Quentis/kee_smart_opener/sw/efr32fg23/config/app_button_press_config.h

/***************************************************************************//**
 * @file
 * @brief
 *******************************************************************************
 * # License
 * <b>Copyright 2021 Silicon Laboratories Inc. www.silabs.com</b>
 *******************************************************************************
 *
 * SPDX-License-Identifier: Zlib
 *
 * The licensor of this software is Silicon Laboratories Inc.
 *
 * This software is provided 'as-is', without any express or implied
 * warranty. In no event will the authors be held liable for any damages
 * arising from the use of this software.
 *
 * Permission is granted to anyone to use this software for any purpose,
 * including commercial applications, and to alter it and redistribute it
 * freely, subject to the following restrictions:
 *
 * 1. The origin of this software must not be misrepresented; you must not
 *    claim that you wrote the original software. If you use this software
 *    in a product, an acknowledgment in the product documentation would be
 *    appreciated but is not required.
 * 2. Altered source versions must be plainly marked as such, and must not be
 *    misrepresented as being the original software.
 * 3. This notice may not be removed or altered from any source distribution.
 *
 ******************************************************************************/
#ifndef APP_BUTTON_PRESS_CONFIG_H
#define APP_BUTTON_PRESS_CONFIG_H

#define APP_BUTTON_PRESS_DETECT_RELEASE (0U)
#define APP_BUTTON_PRESS_DETECT_PRESS_AND_RELEASE (1U)

// <<< Use Configuration Wizard in Context Menu >>>

// <h> Edge Detection

// <o APP_BUTTON_PRESS_DETECTION> Button events to detect by the component
// <APP_BUTTON_PRESS_DETECT_RELEASE=> Button release detection
// <APP_BUTTON_PRESS_DETECT_PRESS_AND_RELEASE=> Button press and release detection
// <i> Default: Button release detection
// <i> By changing this configuration to detect press and release it is necessary to
// increase the command queue size of this component, since more events need to be handled.
#define APP_BUTTON_PRESS_DETECTION      APP_BUTTON_PRESS_DETECT_RELEASE

// </h>

// <h> Threshold values

// <o MIN_VALID_BUTTON_PRESS_DURATION_MS> Minimum duration (ms) of valid button presses
// <i> Default: 40
// <i> Any button press shorter than this value will not be considered as a valid button
// press.
#define MIN_VALID_BUTTON_PRESS_DURATION_MS    (40)

// <o SHORT_BUTTON_PRESS_DURATION_MS> Duration (ms) of Short button presses
// <i> Default: 250
// <i> Any button press shorter than this value and longer than MIN_VALID_BUTTON_PRESS_DURATION_MS
// will be considered SHORT_BUTTON_PRESS.
#define SHORT_BUTTON_PRESS_DURATION_MS   (250)

// <o MEDIUM_BUTTON_PRESS_DURATION_MS> Duration (ms) of MEDIUM button presses
// <i> Default: 1000
// <i> Any button press shorter than this value and longer SHORT_BUTTON_PRESS than will
// be considered MEDIUM_BUTTON_PRESS.
#define MEDIUM_BUTTON_PRESS_DURATION_MS   (1000)

// <o LONG_BUTTON_PRESS_DURATION_MS> Duration (ms) of LONG button presses
// <i> Default: 5000
// <i> Any button press shorter than this value and longer MEDIUM_BUTTON_PRESS than will
// be consideredLONG_BUTTON_PRESS. Any button press longer than this value will be
// considered VERY_LONG_BUTTON_PRESS
#define LONG_BUTTON_PRESS_DURATION_MS   (5000)

// <o APP_BUTTON_PRESS_WAKEUP_DELAY_MS> Duration (ms) from the button press wakeup interrupt to the Sleep Timer initialization
// <i> Default: 0
// <i> This value will be added to the button press timestamp if it caused a wakeup from EM4.
#define APP_BUTTON_PRESS_WAKEUP_DELAY_MS   (0)

// </h>

// <h> Runtime Adaptation

// <o APP_BUTTON_PRESS_CONFIG_PRIORITY> Runtime context priority
// <APP_RTA_PRIORITY_LOW=> Low
// <APP_RTA_PRIORITY_BELOW_NORMAL=> Below normal
// <APP_RTA_PRIORITY_NORMAL=> Normal
// <APP_RTA_PRIORITY_ABOVE_NORMAL=> Above normal
// <APP_RTA_PRIORITY_HIGH=> High
// <i> Default: Normal
// <i> Only takes effect for RTOS.
#define APP_BUTTON_PRESS_CONFIG_PRIORITY           APP_RTA_PRIORITY_NORMAL

// <o APP_BUTTON_PRESS_CONFIG_STACK_SIZE> Stack size (in bytes)
// <i> Default: 1024
// <i> Only takes effect for RTOS.
#define APP_BUTTON_PRESS_CONFIG_STACK_SIZE         (1024)

// <o APP_BUTTON_PRESS_CONFIG_WAIT_FOR_GUARD> Timeout for guard (in ticks)
// <i> Default: 5
// <i> Only takes effect for RTOS.
#define APP_BUTTON_PRESS_CONFIG_WAIT_FOR_GUARD     (5)

// <o APP_BUTTON_PRESS_CONFIG_QUEUE_SIZE> Queue size
// <i> Default: 4
// <i> Queue size for all (bare-metal and RTOS) adaptations.
#define APP_BUTTON_PRESS_CONFIG_QUEUE_SIZE         (4)

// </h>

// <<< end of configuration section >>>

#endif // APP_BUTTON_PRESS_CONFIG_H
