Quentis/kee_smart_opener/sw/efr32fg23/config/pin_config.h

#ifndef PIN_CONFIG_H
#define PIN_CONFIG_H

// $[CMU]
// [CMU]$

// $[LFXO]
// [LFXO]$

// $[PRS.ASYNCH0]
// [PRS.ASYNCH0]$

// $[PRS.ASYNCH1]
// [PRS.ASYNCH1]$

// $[PRS.ASYNCH2]
// [PRS.ASYNCH2]$

// $[PRS.ASYNCH3]
// [PRS.ASYNCH3]$

// $[PRS.ASYNCH4]
// [PRS.ASYNCH4]$

// $[PRS.ASYNCH5]
// [PRS.ASYNCH5]$

// $[PRS.ASYNCH6]
// [PRS.ASYNCH6]$

// $[PRS.ASYNCH7]
// [PRS.ASYNCH7]$

// $[PRS.ASYNCH8]
// [PRS.ASYNCH8]$

// $[PRS.ASYNCH9]
// [PRS.ASYNCH9]$

// $[PRS.ASYNCH10]
// [PRS.ASYNCH10]$

// $[PRS.ASYNCH11]
// [PRS.ASYNCH11]$

// $[PRS.SYNCH0]
// [PRS.SYNCH0]$

// $[PRS.SYNCH1]
// [PRS.SYNCH1]$

// $[PRS.SYNCH2]
// [PRS.SYNCH2]$

// $[PRS.SYNCH3]
// [PRS.SYNCH3]$

// $[GPIO]
// GPIO SWV on PA03
#ifndef GPIO_SWV_PORT                           
#define GPIO_SWV_PORT                            SL_GPIO_PORT_A
#endif
#ifndef GPIO_SWV_PIN                            
#define GPIO_SWV_PIN                             3
#endif

// [GPIO]$

// $[TIMER0]
// TIMER0 CC0 on PD02
#ifndef TIMER0_CC0_PORT                         
#define TIMER0_CC0_PORT                          SL_GPIO_PORT_D
#endif
#ifndef TIMER0_CC0_PIN                          
#define TIMER0_CC0_PIN                           2
#endif

// [TIMER0]$

// $[TIMER1]
// [TIMER1]$

// $[TIMER2]
// [TIMER2]$

// $[TIMER3]
// [TIMER3]$

// $[TIMER4]
// [TIMER4]$

// $[USART0]
// [USART0]$

// $[I2C1]
// [I2C1]$

// $[EUSART1]
// [EUSART1]$

// $[EUSART2]
// [EUSART2]$

// $[LCD]
// [LCD]$

// $[KEYSCAN]
// [KEYSCAN]$

// $[LETIMER0]
// [LETIMER0]$

// $[IADC0]
// [IADC0]$

// $[ACMP0]
// [ACMP0]$

// $[ACMP1]
// [ACMP1]$

// $[VDAC0]
// [VDAC0]$

// $[PCNT0]
// [PCNT0]$

// $[LESENSE]
// [LESENSE]$

// $[HFXO0]
// [HFXO0]$

// $[I2C0]
// [I2C0]$

// $[EUSART0]
// [EUSART0]$

// $[PTI]
// [PTI]$

// $[MODEM]
// [MODEM]$

// $[CUSTOM_PIN_NAME]
#ifndef _PORT                                   
#define _PORT                                    SL_GPIO_PORT_A
#endif
#ifndef _PIN                                    
#define _PIN                                     0
#endif































// [CUSTOM_PIN_NAME]$


#endif // PIN_CONFIG_H
