Quentis/kee_smart_opener/sw/efr32fg23/config/sl_rail_util_init_inst0_config.h

/***************************************************************************//**
 * @file
 * @brief
 *******************************************************************************
 * # License
 * <b>Copyright 2024 Silicon Laboratories Inc. www.silabs.com</b>
 *******************************************************************************
 *
 * SPDX-License-Identifier: Zlib
 *
 * The licensor of this software is Silicon Laboratories Inc.
 *
 * This software is provided 'as-is', without any express or implied
 * warranty. In no event will the authors be held liable for any damages
 * arising from the use of this software.
 *
 * Permission is granted to anyone to use this software for any purpose,
 * including commercial applications, and to alter it and redistribute it
 * freely, subject to the following restrictions:
 *
 * 1. The origin of this software must not be misrepresented; you must not
 *    claim that you wrote the original software. If you use this software
 *    in a product, an acknowledgment in the product documentation would be
 *    appreciated but is not required.
 * 2. Altered source versions must be plainly marked as such, and must not be
 *    misrepresented as being the original software.
 * 3. This notice may not be removed or altered from any source distribution.
 *
 ******************************************************************************/

#ifndef SL_RAIL_UTIL_INIT_INST0_CONFIG_H
#define SL_RAIL_UTIL_INIT_INST0_CONFIG_H

// <<< Use Configuration Wizard in Context Menu >>>

// <h> RAIL Init Configuration
// <e SL_RAIL_UTIL_INIT_INST0_ENABLE> Initialize RAIL
// <i> Default: 1
#define SL_RAIL_UTIL_INIT_INST0_ENABLE 1

// <h> Project Configuration
// <q SL_RAIL_UTIL_INIT_RADIO_CONFIG_SUPPORT_INST0_ENABLE> Enable Radio Configurator Support (include rail_config.c/h generated by Radio Config)
// <i> Default: 0
#define SL_RAIL_UTIL_INIT_RADIO_CONFIG_SUPPORT_INST0_ENABLE 1
// <q SL_RAIL_UTIL_INIT_INIT_COMPLETE_CALLBACK_INST0_ENABLE> Enable RAIL Init Complete Callback
// <i> Default: 0
#define SL_RAIL_UTIL_INIT_INIT_COMPLETE_CALLBACK_INST0_ENABLE 1
// </h>

// <h> FIFO and Queue Configuration
// <h> Receive Packet Queue
// <o SL_RAIL_UTIL_INIT_RX_PACKET_QUEUE_INST0_ENTRIES> Receive Packet Queue Entries
// <-16=>BuiltIn
// <0=>None
// <8=>8
// <16=>16
// <32=>32
// <64=>64
// <128=>128
// <256=>256
// <i> Default: -16
#define SL_RAIL_UTIL_INIT_RX_PACKET_QUEUE_INST0_ENTRIES -16
// </h>
// <h> Receive FIFO
// <o SL_RAIL_UTIL_INIT_RX_FIFO_INST0_BYTES> Receive FIFO Bytes
// <-512=>BuiltIn
// <0=>None
// <64=>64
// <128=>128
// <256=>256
// <512=>512
// <1024=>1024
// <2048=>2048
// <4096=>4096
// <i> Default: -512
#define SL_RAIL_UTIL_INIT_RX_FIFO_INST0_BYTES -512
// </h>
// <h> Transmit FIFO
// <q SL_RAIL_UTIL_INIT_TX_FIFO_INST0_BYTES> Configure initial TX FIFO
// <0=>None
// <64=>64
// <128=>128
// <256=>256
// <512=>512
// <1024=>1024
// <2048=>2048
// <4096=>4096
// <i> Default: 0
#define SL_RAIL_UTIL_INIT_TX_FIFO_INST0_BYTES 256
// </h>
// </h>

// <e SL_RAIL_UTIL_INIT_PROTOCOLS_INST0_ENABLE> Protocol Configuration
// <i> Default: 0
#define SL_RAIL_UTIL_INIT_PROTOCOLS_INST0_ENABLE 1
// <h> Radio Configuration
// <o SL_RAIL_UTIL_INIT_PROTOCOL_INST0_DEFAULT> Default Radio Configuration
// <SL_RAIL_UTIL_PROTOCOL_PROPRIETARY=> Proprietary (use rail_config.c/h)
// <SL_RAIL_UTIL_PROTOCOL_IEEE802154_GB868_915MHZ=> IEEE 802.15.4 GB868 915MHz
// <SL_RAIL_UTIL_PROTOCOL_IEEE802154_GB868_863MHZ=> IEEE 802.15.4 GB868 863MHz
// <SL_RAIL_UTIL_PROTOCOL_ZWAVE_ANZ=> Z-Wave Australia
// <SL_RAIL_UTIL_PROTOCOL_ZWAVE_CN=> Z-Wave China
// <SL_RAIL_UTIL_PROTOCOL_ZWAVE_EU=> Z-Wave Europe
// <SL_RAIL_UTIL_PROTOCOL_ZWAVE_HK=> Z-Wave Hong Kong
// <SL_RAIL_UTIL_PROTOCOL_ZWAVE_IN=> Z-Wave India
// <SL_RAIL_UTIL_PROTOCOL_ZWAVE_IL=> Z-Wave Israel
// <SL_RAIL_UTIL_PROTOCOL_ZWAVE_JP=> Z-Wave Japan
// <SL_RAIL_UTIL_PROTOCOL_ZWAVE_KR=> Z-Wave Korea
// <SL_RAIL_UTIL_PROTOCOL_ZWAVE_MY=> Z-Wave Malaysia
// <SL_RAIL_UTIL_PROTOCOL_ZWAVE_RU=> Z-Wave Russia
// <SL_RAIL_UTIL_PROTOCOL_ZWAVE_US=> Z-Wave United States
// <SL_RAIL_UTIL_PROTOCOL_ZWAVE_US_LR1=> Z-Wave United States, Long Range 1
// <SL_RAIL_UTIL_PROTOCOL_ZWAVE_US_LR2=> Z-Wave United States, Long Range 2
// <SL_RAIL_UTIL_PROTOCOL_ZWAVE_US_LR_END_DEVICE=> Z-Wave United States, Long Range End Device
// <SL_RAIL_UTIL_PROTOCOL_ZWAVE_EU_LR1=> Z-Wave European Union, Long Range 1
// <SL_RAIL_UTIL_PROTOCOL_ZWAVE_EU_LR2=> Z-Wave European Union, Long Range 2
// <SL_RAIL_UTIL_PROTOCOL_ZWAVE_EU_LR_END_DEVICE=> Z-Wave European Union, Long Range End Device
// <i> Default: SL_RAIL_UTIL_PROTOCOL_ZWAVE_EU
#define SL_RAIL_UTIL_INIT_PROTOCOL_INST0_DEFAULT  SL_RAIL_UTIL_PROTOCOL_PROPRIETARY
// <o SL_RAIL_UTIL_INIT_PROTOCOL_PROPRIETARY_INST0_INDEX> Proprietary Radio Config Index (if Proprietary radio config selected, use index X of channelConfigs[X])
// <0-255:1>
// <i> Default: 0
#define SL_RAIL_UTIL_INIT_PROTOCOL_PROPRIETARY_INST0_INDEX 0
// </h>
// </e>

// <e SL_RAIL_UTIL_INIT_CALIBRATIONS_INST0_ENABLE> Calibration Configuration
// <i> Default: 0
#define SL_RAIL_UTIL_INIT_CALIBRATIONS_INST0_ENABLE 1
// <h> Calibration Notifications
// <q SL_RAIL_UTIL_INIT_CALIBRATION_TEMPERATURE_NOTIFY_INST0_ENABLE> Enable Temperature Calibration Notifications (RAIL_EVENT_CAL_NEEDED radio event issued when temperature calibrations needed, for example VCO calibration)
// <i> Default: 0
#define SL_RAIL_UTIL_INIT_CALIBRATION_TEMPERATURE_NOTIFY_INST0_ENABLE 1
// <q SL_RAIL_UTIL_INIT_CALIBRATION_ONETIME_NOTIFY_INST0_ENABLE> Enable One-time Calibration Notifications (RAIL_EVENT_CAL_NEEDED radio event issued when one-time calibrations needed, for example IR calibration)
// <i> Default: 0
#define SL_RAIL_UTIL_INIT_CALIBRATION_ONETIME_NOTIFY_INST0_ENABLE 1
// </h>
// </e>

// <e SL_RAIL_UTIL_INIT_TRANSITIONS_INST0_ENABLE> Auto Transition Configuration
// <i> Default: 0
#define SL_RAIL_UTIL_INIT_TRANSITIONS_INST0_ENABLE 1
// <h> TX Transitions
// <o SL_RAIL_UTIL_INIT_TRANSITION_INST0_TX_SUCCESS> Transition on TX Success
// <RAIL_RF_STATE_RX=> RX
// <RAIL_RF_STATE_IDLE=> Idle
// <i> Default: RAIL_RF_STATE_IDLE
#define SL_RAIL_UTIL_INIT_TRANSITION_INST0_TX_SUCCESS  RAIL_RF_STATE_IDLE
// <o SL_RAIL_UTIL_INIT_TRANSITION_INST0_TX_ERROR> Transition on TX Error
// <RAIL_RF_STATE_RX=> RX
// <RAIL_RF_STATE_IDLE=> Idle
// <i> Default: RAIL_RF_STATE_IDLE
#define SL_RAIL_UTIL_INIT_TRANSITION_INST0_TX_ERROR  RAIL_RF_STATE_IDLE
// </h>
// <h> RX Transitions
// <o SL_RAIL_UTIL_INIT_TRANSITION_INST0_RX_SUCCESS> Transition on RX Success
// <RAIL_RF_STATE_RX=> RX
// <RAIL_RF_STATE_TX=> TX
// <RAIL_RF_STATE_IDLE=> Idle
// <i> Default: RAIL_RF_STATE_IDLE
#define SL_RAIL_UTIL_INIT_TRANSITION_INST0_RX_SUCCESS  RAIL_RF_STATE_IDLE
// <o SL_RAIL_UTIL_INIT_TRANSITION_INST0_RX_ERROR> Transition on RX Error
// <RAIL_RF_STATE_RX=> RX
// <RAIL_RF_STATE_IDLE=> Idle
// <i> Default: RAIL_RF_STATE_IDLE
#define SL_RAIL_UTIL_INIT_TRANSITION_INST0_RX_ERROR  RAIL_RF_STATE_IDLE
// </h>
// </e>

// <e SL_RAIL_UTIL_INIT_TX_DATA_FORMAT_INST0_ENABLE> TX Data Format Configuration
// <i> Default: 0
#define SL_RAIL_UTIL_INIT_TX_DATA_FORMAT_INST0_ENABLE 0
// <h> TX Data
// <o SL_RAIL_UTIL_INIT_TX_DATA_FORMAT_INST0_SOURCE> Source of TX Data
// <SL_RAIL_TX_DATA_SOURCE_PACKET_DATA=> Use frame hardware to packetize data
// <i> Default: SL_RAIL_TX_DATA_SOURCE_PACKET_DATA
#define SL_RAIL_UTIL_INIT_TX_DATA_FORMAT_INST0_SOURCE  SL_RAIL_TX_DATA_SOURCE_PACKET_DATA
// <o SL_RAIL_UTIL_INIT_TX_DATA_FORMAT_INST0_MODE> Method of Providing TX Data
// <SL_RAIL_DATA_METHOD_PACKET_MODE=> Packet Mode
// <SL_RAIL_DATA_METHOD_FIFO_MODE=> FIFO Mode
// <i> Default: SL_RAIL_DATA_METHOD_PACKET_MODE
#define SL_RAIL_UTIL_INIT_TX_DATA_FORMAT_INST0_MODE  SL_RAIL_DATA_METHOD_PACKET_MODE
// </h>
// </e>

// <e SL_RAIL_UTIL_INIT_RX_DATA_FORMAT_INST0_ENABLE> RX Data Format Configuration
// <i> Default: 0
#define SL_RAIL_UTIL_INIT_RX_DATA_FORMAT_INST0_ENABLE 0
// <h> RX Data
// <o SL_RAIL_UTIL_INIT_RX_DATA_FORMAT_INST0_SOURCE> Source of RX Data
// <SL_RAIL_RX_DATA_SOURCE_PACKET_DATA=> Use frame hardware to packetize data
// <SL_RAIL_RX_DATA_SOURCE_DEMOD_DATA=> Get 8-bit output from demodulator
// <SL_RAIL_RX_DATA_SOURCE_IQDATA_FILTLSB=> Get lowest 16 bits of I/Q data provided to demodulator
// <SL_RAIL_RX_DATA_SOURCE_IQDATA_FILTMSB=> Get highest 16 bits of I/Q data provided to demodulator
// <i> Default: SL_RAIL_RX_DATA_SOURCE_PACKET_DATA
#define SL_RAIL_UTIL_INIT_RX_DATA_FORMAT_INST0_SOURCE  SL_RAIL_RX_DATA_SOURCE_PACKET_DATA
// <o SL_RAIL_UTIL_INIT_RX_DATA_FORMAT_INST0_MODE> Method of Retrieving RX Data
// <SL_RAIL_DATA_METHOD_PACKET_MODE=> Packet Mode
// <SL_RAIL_DATA_METHOD_FIFO_MODE=> FIFO Mode
// <i> Default: SL_RAIL_DATA_METHOD_PACKET_MODE
#define SL_RAIL_UTIL_INIT_RX_DATA_FORMAT_INST0_MODE  SL_RAIL_DATA_METHOD_PACKET_MODE
// </h>
// </e>

// <e SL_RAIL_UTIL_INIT_EVENTS_INST0_ENABLE> Radio Event Configuration
// <i> Default: 0
#define SL_RAIL_UTIL_INIT_EVENTS_INST0_ENABLE 1
// <h> RX Radio Events
// <q SL_RAIL_UTIL_INIT_EVENT_RX_TIMING_DETECT_INST0_ENABLE> RX Timing Detect
// <i> Default: 0
#define SL_RAIL_UTIL_INIT_EVENT_RX_TIMING_DETECT_INST0_ENABLE 1
// <q SL_RAIL_UTIL_INIT_EVENT_RX_TIMING_LOST_INST0_ENABLE> RX Timing Lost
// <i> Default: 0
#define SL_RAIL_UTIL_INIT_EVENT_RX_TIMING_LOST_INST0_ENABLE 1
// <q SL_RAIL_UTIL_INIT_EVENT_RX_PREAMBLE_DETECT_INST0_ENABLE> RX Preamble Detect
// <i> Default: 0
#define SL_RAIL_UTIL_INIT_EVENT_RX_PREAMBLE_DETECT_INST0_ENABLE 1
// <q SL_RAIL_UTIL_INIT_EVENT_RX_PREAMBLE_LOST_INST0_ENABLE> RX Preamble Lost
// <i> Default: 0
#define SL_RAIL_UTIL_INIT_EVENT_RX_PREAMBLE_LOST_INST0_ENABLE 1
// <q SL_RAIL_UTIL_INIT_EVENT_RX_SYNC_0_DETECT_INST0_ENABLE> RX Sync0 Detect
// <i> Default: 0
#define SL_RAIL_UTIL_INIT_EVENT_RX_SYNC_0_DETECT_INST0_ENABLE 0
// <q SL_RAIL_UTIL_INIT_EVENT_RX_SYNC_1_DETECT_INST0_ENABLE> RX Sync1 Detect
// <i> Default: 0
#define SL_RAIL_UTIL_INIT_EVENT_RX_SYNC_1_DETECT_INST0_ENABLE 0
// <q SL_RAIL_UTIL_INIT_EVENT_RX_FILTER_PASSED_INST0_ENABLE> RX Filter Passed
// <i> Default: 0
#define SL_RAIL_UTIL_INIT_EVENT_RX_FILTER_PASSED_INST0_ENABLE 1
// <q SL_RAIL_UTIL_INIT_EVENT_RX_ADDRESS_FILTERED_INST0_ENABLE> RX Address Filtered
// <i> Default: 0
#define SL_RAIL_UTIL_INIT_EVENT_RX_ADDRESS_FILTERED_INST0_ENABLE 1
// <q SL_RAIL_UTIL_INIT_EVENT_RX_PACKET_RECEIVED_INST0_ENABLE> RX Packet Received
// <i> Default: 0
#define SL_RAIL_UTIL_INIT_EVENT_RX_PACKET_RECEIVED_INST0_ENABLE 1
// <q SL_RAIL_UTIL_INIT_EVENT_RX_FRAME_ERROR_INST0_ENABLE> RX Frame Error
// <i> Default: 0
#define SL_RAIL_UTIL_INIT_EVENT_RX_FRAME_ERROR_INST0_ENABLE 1
// <q SL_RAIL_UTIL_INIT_EVENT_RX_PACKET_ABORTED_INST0_ENABLE> RX Packet Aborted
// <i> Default: 0
#define SL_RAIL_UTIL_INIT_EVENT_RX_PACKET_ABORTED_INST0_ENABLE 1
// <q SL_RAIL_UTIL_INIT_EVENT_RX_TIMEOUT_INST0_ENABLE> RX Timeout
// <i> Default: 0
#define SL_RAIL_UTIL_INIT_EVENT_RX_TIMEOUT_INST0_ENABLE 1
// <q SL_RAIL_UTIL_INIT_EVENT_RX_CHANNEL_HOPPING_COMPLETE_INST0_ENABLE> RX Channel Hopping Complete
// <i> Default: 0
#define SL_RAIL_UTIL_INIT_EVENT_RX_CHANNEL_HOPPING_COMPLETE_INST0_ENABLE 1
// <q SL_RAIL_UTIL_INIT_EVENT_RX_DUTY_CYCLE_RX_END_INST0_ENABLE> RX Duty Cycle RX End
// <i> Default: 0
#define SL_RAIL_UTIL_INIT_EVENT_RX_DUTY_CYCLE_RX_END_INST0_ENABLE 1
// </h>
// <h> TX Radio Events
// <q SL_RAIL_UTIL_INIT_EVENT_TX_PACKET_SENT_INST0_ENABLE> TX Packet Sent
// <i> Default: 0
#define SL_RAIL_UTIL_INIT_EVENT_TX_PACKET_SENT_INST0_ENABLE 1
// <q SL_RAIL_UTIL_INIT_EVENT_TX_ABORTED_INST0_ENABLE> TX Aborted
// <i> Default: 0
#define SL_RAIL_UTIL_INIT_EVENT_TX_ABORTED_INST0_ENABLE 1
// <q SL_RAIL_UTIL_INIT_EVENT_TX_BLOCKED_INST0_ENABLE> TX Blocked
// <i> Default: 0
#define SL_RAIL_UTIL_INIT_EVENT_TX_BLOCKED_INST0_ENABLE 1
// <q SL_RAIL_UTIL_INIT_EVENT_TX_STARTED_INST0_ENABLE> TX Started
// <i> Default: 0
#define SL_RAIL_UTIL_INIT_EVENT_TX_STARTED_INST0_ENABLE 1
// </h>
// <h> RSSI Radio Events
// <q SL_RAIL_UTIL_INIT_EVENT_RSSI_AVERAGE_DONE_INST0_ENABLE> RSSI Average Done
// <i> Default: 0
#define SL_RAIL_UTIL_INIT_EVENT_RSSI_AVERAGE_DONE_INST0_ENABLE 1
// </h>
// <h> FIFO Radio Events
// <q SL_RAIL_UTIL_INIT_EVENT_RX_FIFO_ALMOST_FULL_INST0_ENABLE> RX FIFO, Almost Full
// <i> Default: 0
#define SL_RAIL_UTIL_INIT_EVENT_RX_FIFO_ALMOST_FULL_INST0_ENABLE 1
// <q SL_RAIL_UTIL_INIT_EVENT_RX_FIFO_FULL_INST0_ENABLE> RX FIFO, Full
// <i> Default: 0
#define SL_RAIL_UTIL_INIT_EVENT_RX_FIFO_FULL_INST0_ENABLE 1
// <q SL_RAIL_UTIL_INIT_EVENT_RX_FIFO_OVERFLOW_INST0_ENABLE> RX FIFO, Overflow
// <i> Default: 0
#define SL_RAIL_UTIL_INIT_EVENT_RX_FIFO_OVERFLOW_INST0_ENABLE 1
// <q SL_RAIL_UTIL_INIT_EVENT_TX_FIFO_ALMOST_EMPTY_INST0_ENABLE> TX FIFO, Almost Empty
// <i> Default: 0
#define SL_RAIL_UTIL_INIT_EVENT_TX_FIFO_ALMOST_EMPTY_INST0_ENABLE 1
// <q SL_RAIL_UTIL_INIT_EVENT_TX_UNDERFLOW_INST0_ENABLE> TX FIFO, Underflow
// <i> Default: 0
#define SL_RAIL_UTIL_INIT_EVENT_TX_UNDERFLOW_INST0_ENABLE 1
// </h>
// <h> CCA Radio Events
// <q SL_RAIL_UTIL_INIT_EVENT_TX_CHANNEL_CLEAR_INST0_ENABLE> TX CCA, Channel Clear
// <i> Default: 0
#define SL_RAIL_UTIL_INIT_EVENT_TX_CHANNEL_CLEAR_INST0_ENABLE 1
// <q SL_RAIL_UTIL_INIT_EVENT_TX_CHANNEL_BUSY_INST0_ENABLE> TX CCA, Channel Busy
// <i> Default: 0
#define SL_RAIL_UTIL_INIT_EVENT_TX_CHANNEL_BUSY_INST0_ENABLE 1
// <q SL_RAIL_UTIL_INIT_EVENT_TX_CCA_RETRY_INST0_ENABLE> TX CCA, Retry
// <i> Default: 0
#define SL_RAIL_UTIL_INIT_EVENT_TX_CCA_RETRY_INST0_ENABLE 1
// <q SL_RAIL_UTIL_INIT_EVENT_TX_START_CCA_INST0_ENABLE> TX CCA, Started
// <i> Default: 0
#define SL_RAIL_UTIL_INIT_EVENT_TX_START_CCA_INST0_ENABLE 1
// </h>
// <h> Scheduled Radio Events
// <q SL_RAIL_UTIL_INIT_EVENT_RX_TX_SCHEDULED_RX_TX_STARTED_INST0_ENABLE> Scheduled RX/TX Started
// <i> Default: 0
#define SL_RAIL_UTIL_INIT_EVENT_RX_TX_SCHEDULED_RX_TX_STARTED_INST0_ENABLE 1
// <q SL_RAIL_UTIL_INIT_EVENT_RX_SCHEDULED_RX_END_INST0_ENABLE> Scheduled RX End
// <i> Default: 0
#define SL_RAIL_UTIL_INIT_EVENT_RX_SCHEDULED_RX_END_INST0_ENABLE 1
// <q SL_RAIL_UTIL_INIT_EVENT_RX_SCHEDULED_RX_MISSED_INST0_ENABLE> Scheduled RX Missed
// <i> Default: 0
#define SL_RAIL_UTIL_INIT_EVENT_RX_SCHEDULED_RX_MISSED_INST0_ENABLE 1
// <q SL_RAIL_UTIL_INIT_EVENT_TX_SCHEDULED_TX_MISSED_INST0_ENABLE> Scheduled TX Missed
// <i> Default: 0
#define SL_RAIL_UTIL_INIT_EVENT_TX_SCHEDULED_TX_MISSED_INST0_ENABLE 1
// </h>
// <h> ACK Radio Events
// <q SL_RAIL_UTIL_INIT_EVENT_RX_ACK_TIMEOUT_INST0_ENABLE> RX ACK, Timeout
// <i> Default: 0
#define SL_RAIL_UTIL_INIT_EVENT_RX_ACK_TIMEOUT_INST0_ENABLE 1
// <q SL_RAIL_UTIL_INIT_EVENT_TXACK_PACKET_SENT_INST0_ENABLE> TX ACK, Packet Sent
// <i> Default: 0
#define SL_RAIL_UTIL_INIT_EVENT_TXACK_PACKET_SENT_INST0_ENABLE 1
// <q SL_RAIL_UTIL_INIT_EVENT_TXACK_ABORTED_INST0_ENABLE> TX ACK, Aborted
// <i> Default: 0
#define SL_RAIL_UTIL_INIT_EVENT_TXACK_ABORTED_INST0_ENABLE 1
// <q SL_RAIL_UTIL_INIT_EVENT_TXACK_BLOCKED_INST0_ENABLE> TX ACK, Blocked
// <i> Default: 0
#define SL_RAIL_UTIL_INIT_EVENT_TXACK_BLOCKED_INST0_ENABLE 1
// <q SL_RAIL_UTIL_INIT_EVENT_TXACK_UNDERFLOW_INST0_ENABLE> TX ACK, FIFO Underflow
// <i> Default: 0
#define SL_RAIL_UTIL_INIT_EVENT_TXACK_UNDERFLOW_INST0_ENABLE 1
// </h>
// <h> Protocol Radio Events
// <q SL_RAIL_UTIL_INIT_EVENT_IEEE802154_DATA_REQUEST_COMMAND_INST0_ENABLE> IEEE 802.15.4 Data Request Command
// <i> Default: 0
#define SL_RAIL_UTIL_INIT_EVENT_IEEE802154_DATA_REQUEST_COMMAND_INST0_ENABLE 1
// <q SL_RAIL_UTIL_INIT_EVENT_ZWAVE_BEAM_INST0_ENABLE> Z-Wave Beam
// <i> Default: 0
#define SL_RAIL_UTIL_INIT_EVENT_ZWAVE_BEAM_INST0_ENABLE 1
// <q SL_RAIL_UTIL_INIT_EVENT_ZWAVE_LR_ACK_REQUEST_COMMAND_INST0_ENABLE> Z-Wave LR ACK Request Command
// <i> Default: 0
#define SL_RAIL_UTIL_INIT_EVENT_ZWAVE_LR_ACK_REQUEST_COMMAND_INST0_ENABLE 0
// </h>
// <h> Dynamic Multiprotocol (DMP) Radio Events
// <q SL_RAIL_UTIL_INIT_EVENT_CONFIG_UNSCHEDULED_INST0_ENABLE> Config Unscheduled
// <i> Default: 0
#define SL_RAIL_UTIL_INIT_EVENT_CONFIG_UNSCHEDULED_INST0_ENABLE 1
// <q SL_RAIL_UTIL_INIT_EVENT_CONFIG_SCHEDULED_INST0_ENABLE> Config Scheduled
// <i> Default: 0
#define SL_RAIL_UTIL_INIT_EVENT_CONFIG_SCHEDULED_INST0_ENABLE 1
// <q SL_RAIL_UTIL_INIT_EVENT_SCHEDULER_STATUS_INST0_ENABLE> Scheduler Status
// <i> Default: 0
#define SL_RAIL_UTIL_INIT_EVENT_SCHEDULER_STATUS_INST0_ENABLE 1
// </h>
// <h> Calibration Radio Events
// <q SL_RAIL_UTIL_INIT_EVENT_CAL_NEEDED_INST0_ENABLE> Calibration Needed
// <i> Default: 0
#define SL_RAIL_UTIL_INIT_EVENT_CAL_NEEDED_INST0_ENABLE 1
// </h>
// <h> RSSI Radio Events
// <q SL_RAIL_UTIL_INIT_EVENT_DETECT_RSSI_THRESHOLD_INST0_ENABLE> RSSI detect threshold
// <i> Default: 0
#define SL_RAIL_UTIL_INIT_EVENT_DETECT_RSSI_THRESHOLD_INST0_ENABLE 0
// </h>
// <h> Thermistor Events
// <q SL_RAIL_UTIL_INIT_EVENT_THERMISTOR_DONE_INST0_ENABLE> End of thermistor measurement
// <i> Default: 0
#define SL_RAIL_UTIL_INIT_EVENT_THERMISTOR_DONE_INST0_ENABLE 0
// </h>
// <h> Temperature Events
// <q SL_RAIL_UTIL_INIT_EVENT_TEMPERATURE_TOO_HOT_INST0_ENABLE> Temperature is too hot for Tx operation
// <i> Default: 0
#define SL_RAIL_UTIL_INIT_EVENT_TEMPERATURE_TOO_HOT_INST0_ENABLE 0
// <q SL_RAIL_UTIL_INIT_EVENT_TEMPERATURE_COOL_DOWN_INST0_ENABLE> Temperature has cooled enough for Tx operation
// <i> Default: 0
#define SL_RAIL_UTIL_INIT_EVENT_TEMPERATURE_COOL_DOWN_INST0_ENABLE 0
// </h>
// </e>

// </e>
// </h>

// <<< end of configuration section >>>

#endif // SL_RAIL_UTIL_INIT_INST0_CONFIG_H
